Petrusov/enviromental-measurement-esp32-solarpowered/Bitmaps/Blokove_schema.png

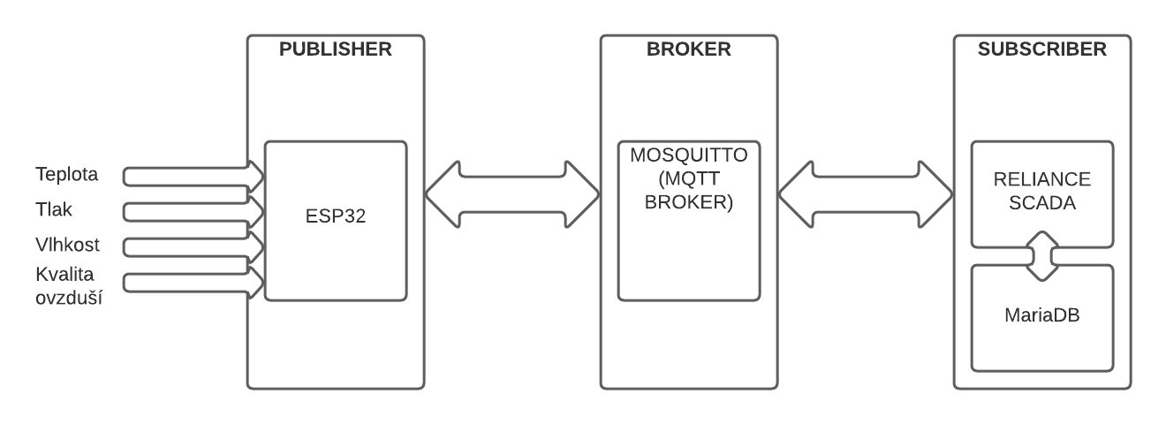
Bitmaps/Blokove_schema.png
