Petrusov/enviromental-measurement-esp32-solarpowered/Bitmaps/Blokove_schema_esp32.png

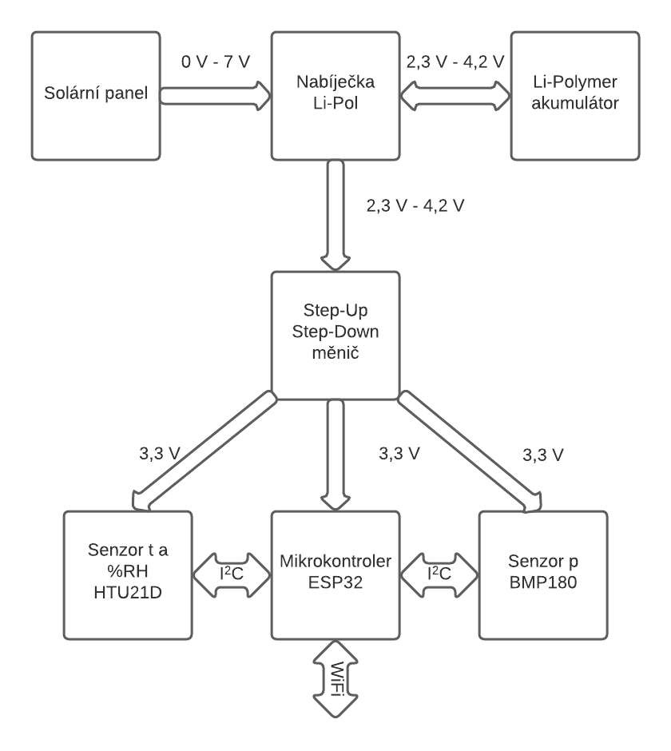
Bitmaps/Blokove_schema_esp32.png
