Petrusov/enviromental-measurement-esp32-solarpowered/Bitmaps/MQTT Explorer - Client.png

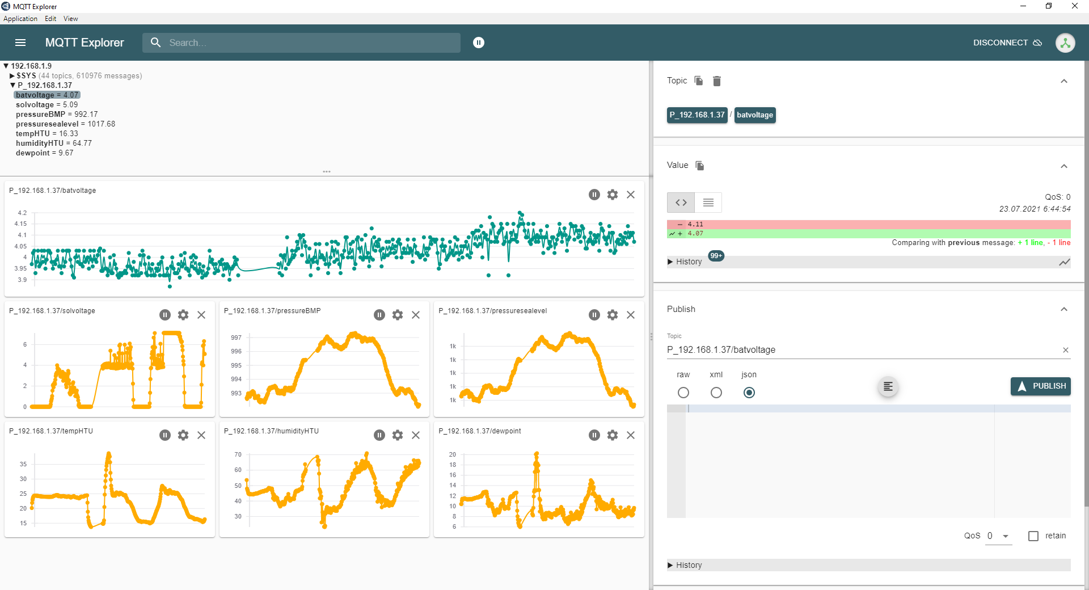
Bitmaps/MQTT Explorer - Client.png
