Petrusov/enviromental-measurement-esp32-solarpowered/Bitmaps/MQTT Explorer - Client_2.png

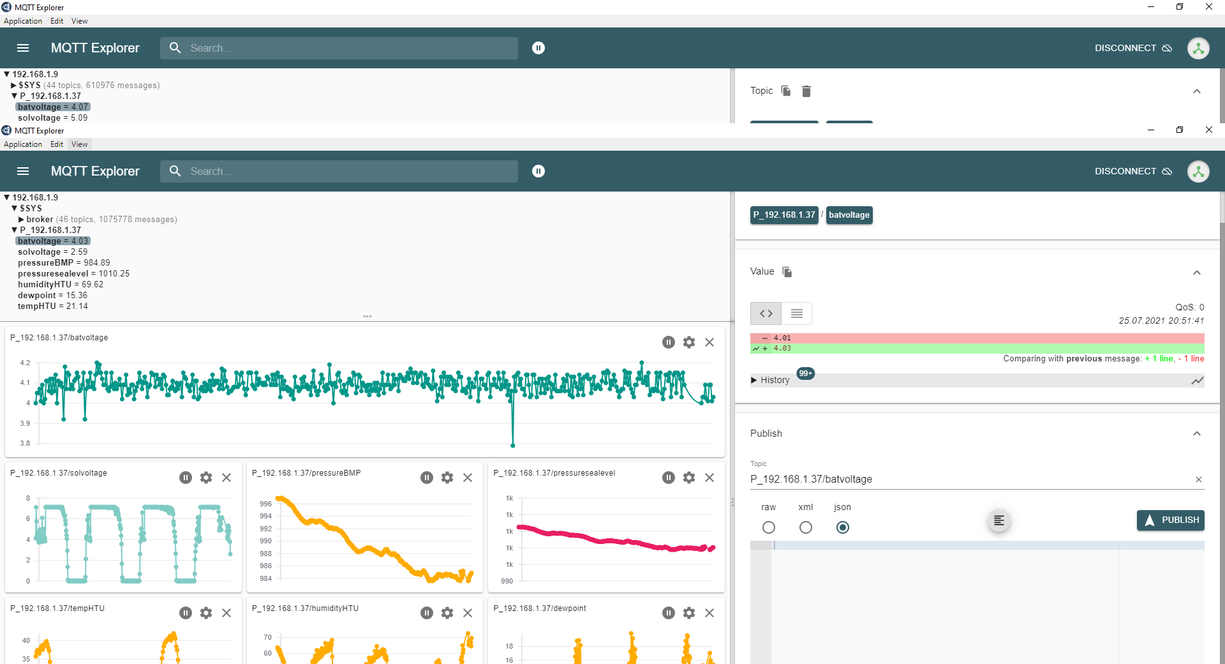
Bitmaps/MQTT Explorer - Client_2.png
