Petrusov/enviromental-measurement-esp32-solarpowered/Bitmaps/MQTT Explorer - Client_3.png

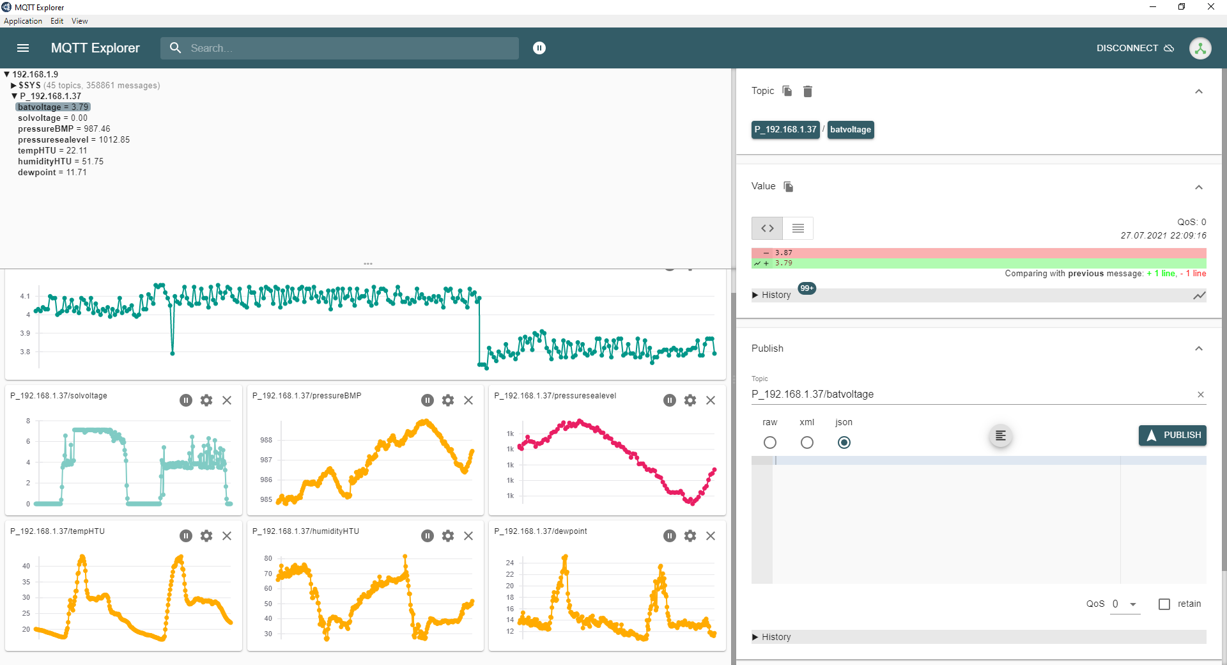
Bitmaps/MQTT Explorer - Client_3.png
