Petrusov/enviromental-measurement-esp32-solarpowered/Bitmaps/MQTT_komunikace.png

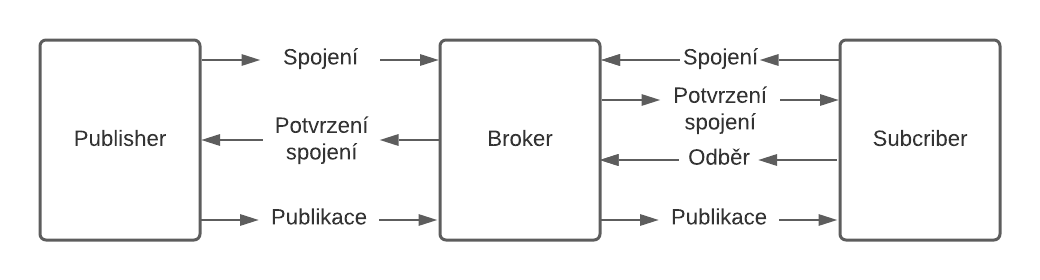
Bitmaps/MQTT_komunikace.png
