Petrusov/enviromental-measurement-esp32-solarpowered/Bitmaps/Reliance1.png

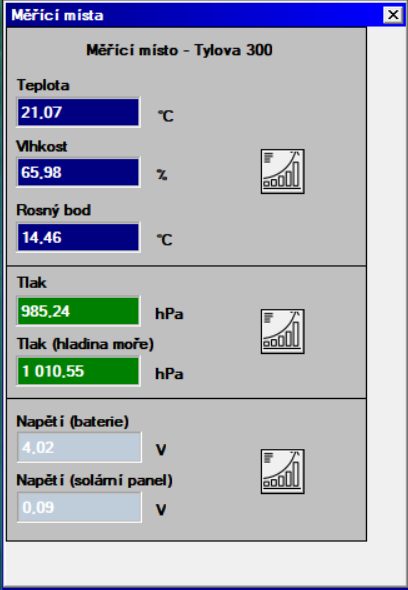
Bitmaps/Reliance1.png
