Petrusov/enviromental-measurement-esp32-solarpowered/Bitmaps/Reliance2.png

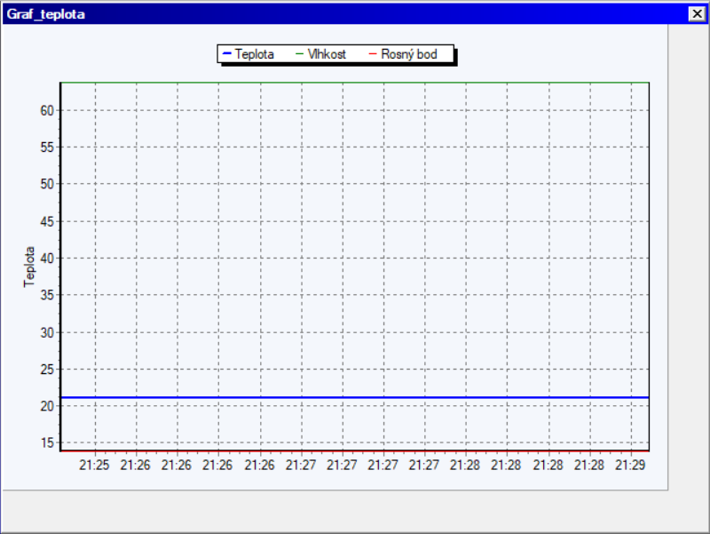
Bitmaps/Reliance2.png
