Petrusov/enviromental-measurement-esp32-solarpowered/Bitmaps/Reliance3.png

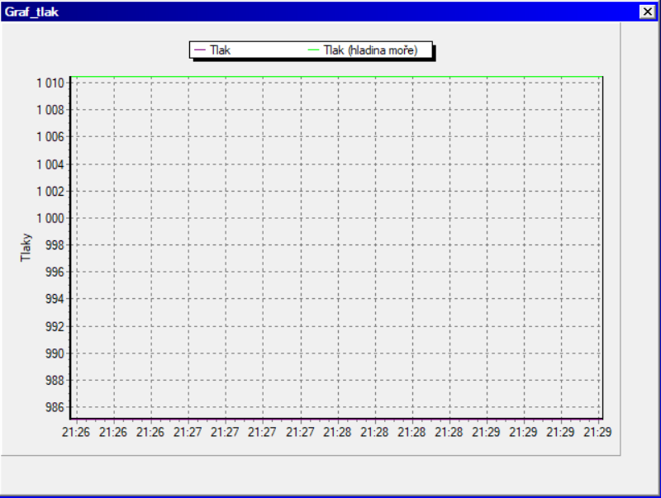
Bitmaps/Reliance3.png
