Petrusov/enviromental-measurement-esp32-solarpowered/Bitmaps/Reliance4.png

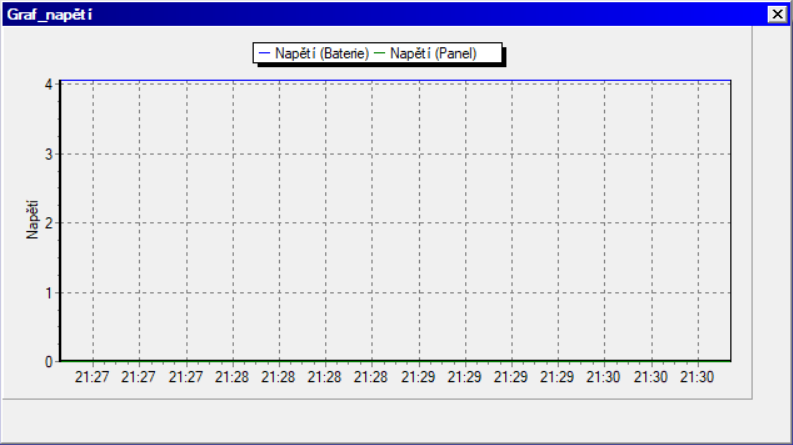
Bitmaps/Reliance4.png
