Petrusov/enviromental-measurement-esp32-solarpowered/Bitmaps/Reliance6.png

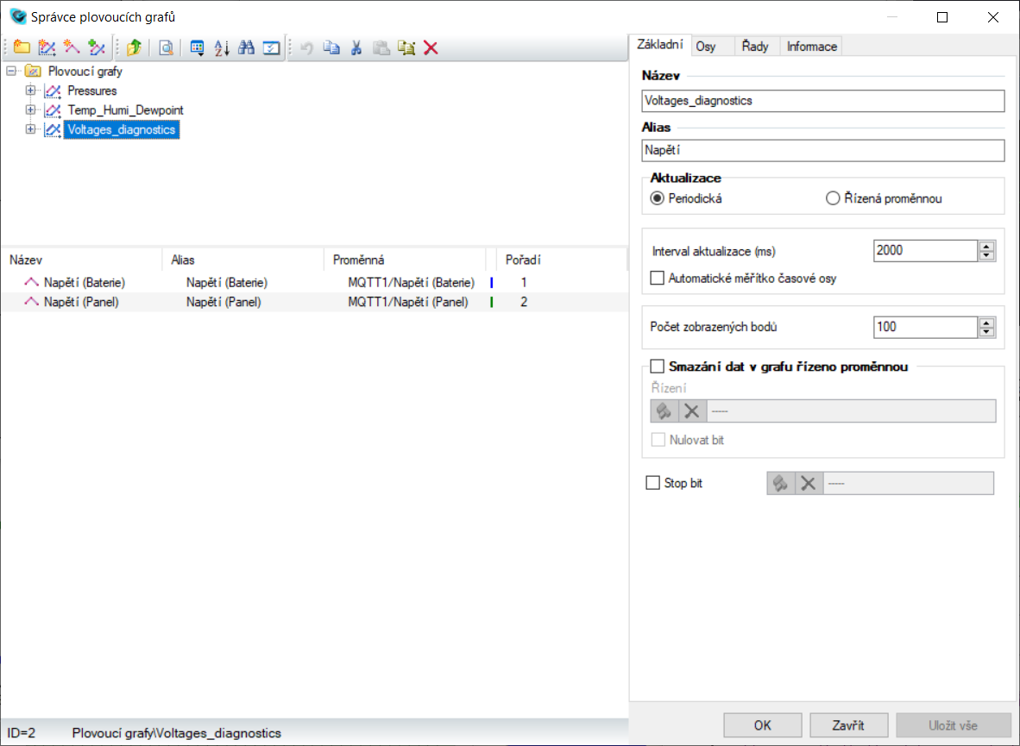
Bitmaps/Reliance6.png
