Petrusov/enviromental-measurement-esp32-solarpowered/Bitmaps/Reliance7.png

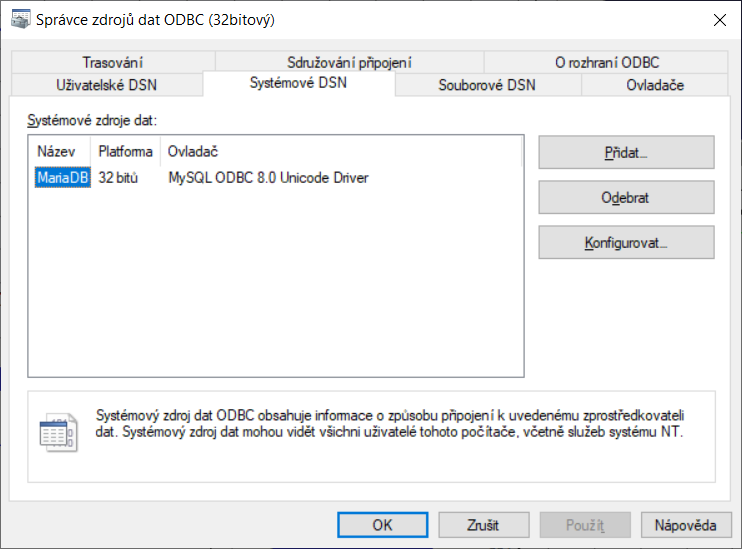
Bitmaps/Reliance7.png
