Petrusov/enviromental-measurement-esp32-solarpowered/Bitmaps/Seeback.png

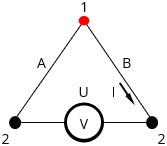
Bitmaps/Seeback.png
